PrabathBK/Water-Quality-Measure-Device/Project_enclousure/Final/Enclosure Part 1.SLDPRT

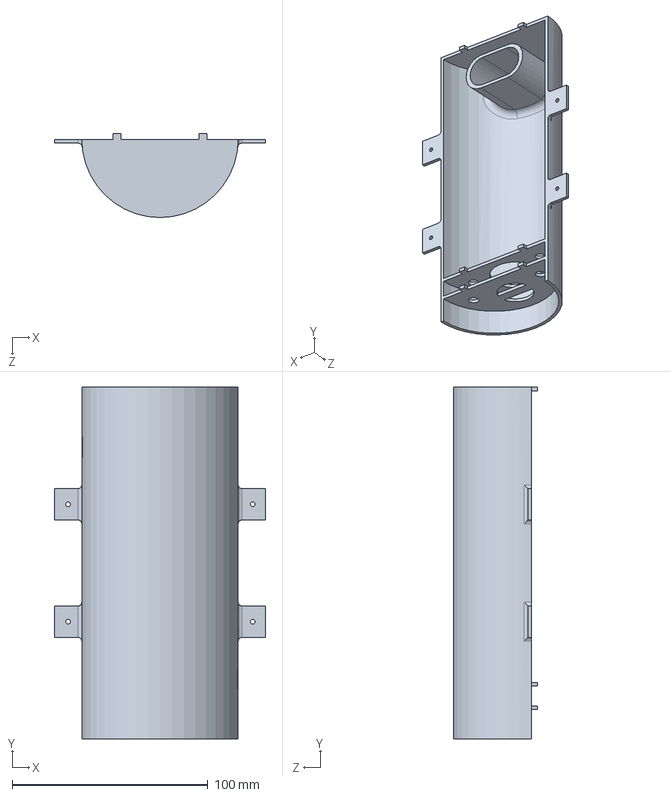
[picture p59: CAD file, 2024-04-02]
Project_enclousure/Final/Enclosure Part 1.SLDPRT
108.0 x 180.0 x 43.0 mm
