PrabathBK/Water-Quality-Measure-Device/Project_enclousure/Final/Enclousure Part 2.SLDPRT

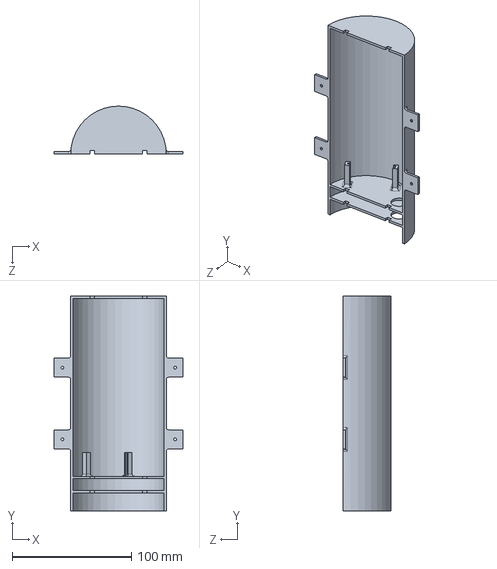
[picture p60: CAD file, 2024-04-02]
Project_enclousure/Final/Enclousure Part 2.SLDPRT
108.0 x 180.0 x 40.0 mm
