PrabathBK/Water-Quality-Measure-Device/Project_enclousure/Sensors/TDS_sensor.SLDPRT

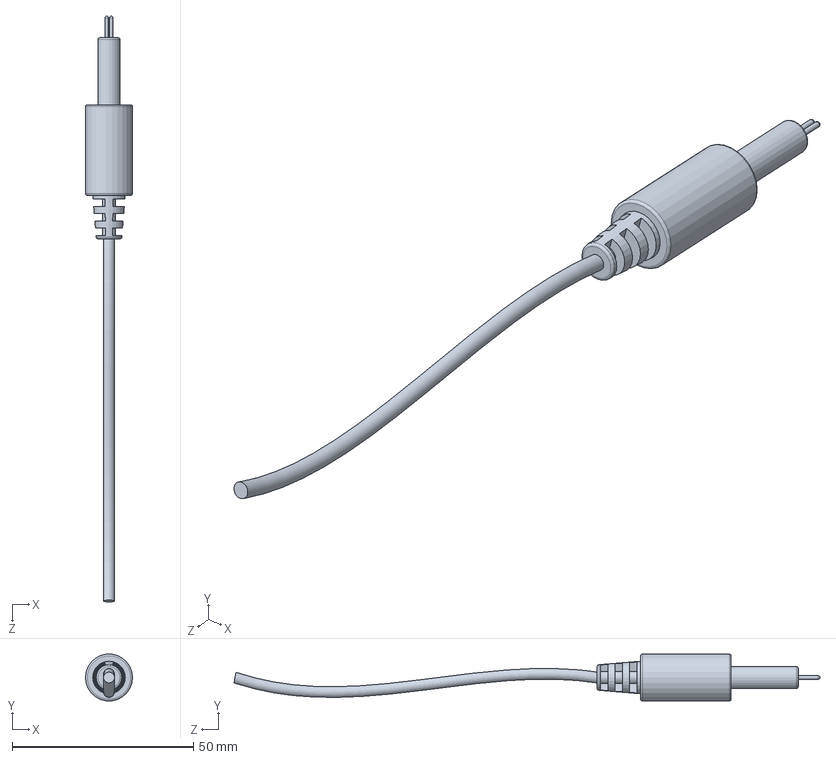
[picture p61: CAD file, 2024-04-01]
Project_enclousure/Sensors/TDS_sensor.SLDPRT
13.0 x 12.9 x 161.7 mm
