PrabathBK/Water-Quality-Measure-Device/Project_enclousure/Sensors/Temp_sensor.SLDPRT

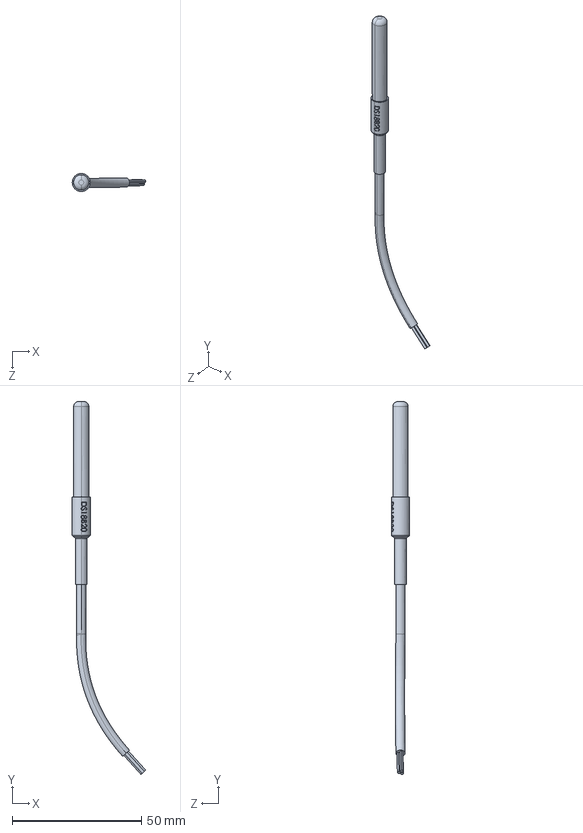
[picture p62: CAD file, 2024-04-01]
Project_enclousure/Sensors/Temp_sensor.SLDPRT
28.5 x 144.6 x 7.00 mm
