PrabathBK/Water-Quality-Measure-Device/Project_enclousure/Enclousure2.SLDPRT

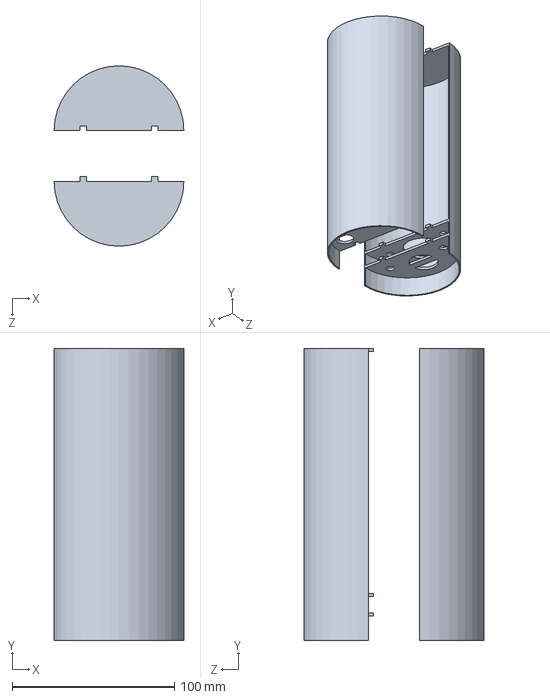
[picture p63: CAD file, 2024-04-01]
Project_enclousure/Enclousure2.SLDPRT
80.0 x 180.0 x 111.2 mm
