PrabathBK/Water-Quality-Measure-Device/Project_enclousure/Sensors/ph_probe.SLDPRT

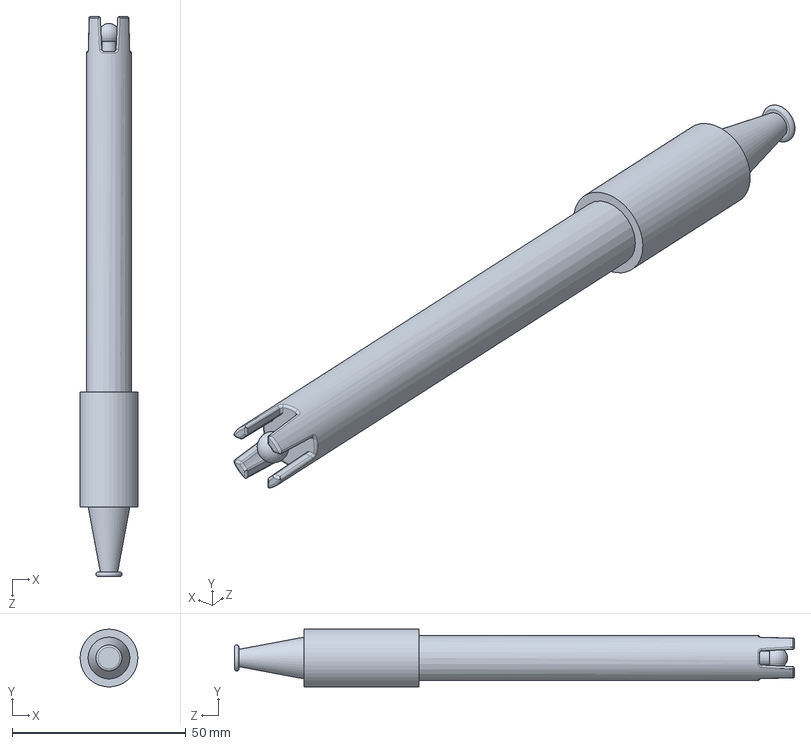
[picture p64: CAD file, 2024-04-01]
Project_enclousure/Sensors/ph_probe.SLDPRT
16.6 x 16.6 x 161.0 mm
