PrabathBK/Water-Quality-Measure-Device/Project_enclousure/Enclousure!.SLDPRT

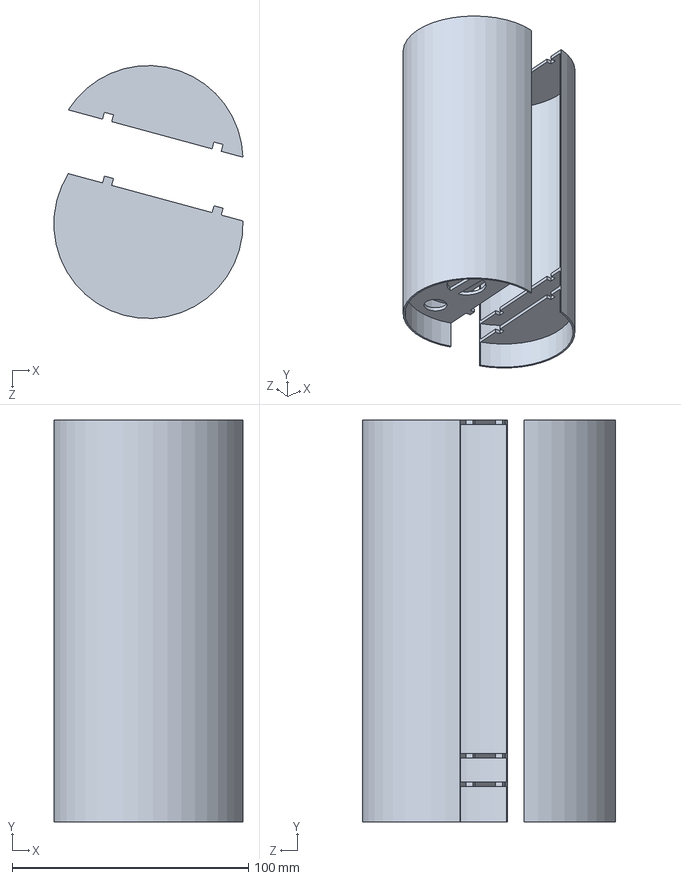
[picture p65: CAD file, 2024-04-01]
Project_enclousure/Enclousure!.SLDPRT
79.9 x 170.0 x 106.9 mm
