PrabathBK/Water-Quality-Measure-Device/Project_enclousure/PCB.SLDPRT

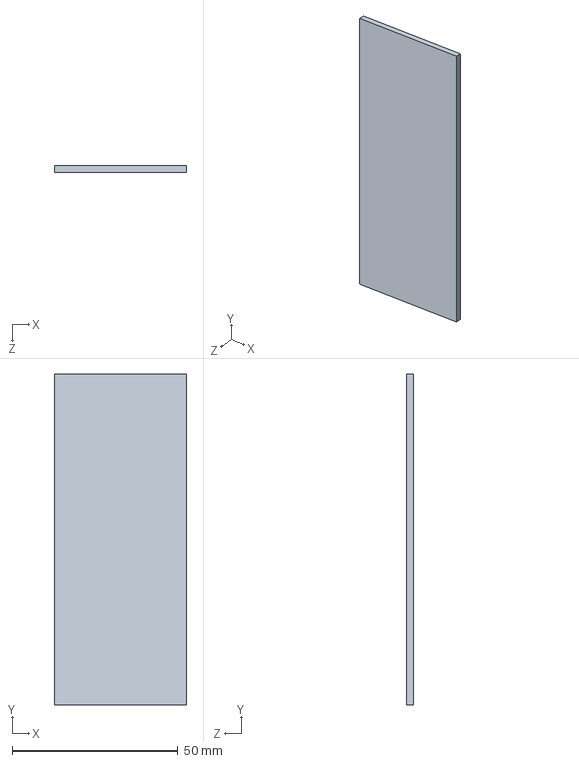
[picture p66: CAD file, 2024-04-01]
Project_enclousure/PCB.SLDPRT
40.0 x 100.0 x 2.00 mm
